ndNgoc1310/Embedded-System-Project/3. Firmware Design/Mylibrary/inc/GUI_Paint.h

/******************************************************************************
* | File      	:   GUI_Paint.h
* | Author      :   Waveshare electronics
* | Function    :	Achieve drawing: draw points, lines, boxes, circles and
*                   their size, solid dotted line, solid rectangle hollow
*                   rectangle, solid circle hollow circle.
* | Info        :
*   Achieve display characters: Display a single character, string, number
*   Achieve time display: adaptive size display time minutes and seconds
*----------------
* |	This version:   V3.0
* | Date        :   2019-04-18
* | Info        :
* -----------------------------------------------------------------------------
* V3.0(2019-04-18):
* 1.Change: 
*    Paint_DrawPoint(..., DOT_STYLE DOT_STYLE)
* => Paint_DrawPoint(..., DOT_STYLE Dot_Style)
*    Paint_DrawLine(..., LINE_STYLE Line_Style, DOT_PIXEL Dot_Pixel)
* => Paint_DrawLine(..., DOT_PIXEL Line_width, LINE_STYLE Line_Style)
*    Paint_DrawRectangle(..., DRAW_FILL Filled, DOT_PIXEL Dot_Pixel)
* => Paint_DrawRectangle(..., DOT_PIXEL Line_width, DRAW_FILL Draw_Fill)
*    Paint_DrawCircle(..., DRAW_FILL Draw_Fill, DOT_PIXEL Dot_Pixel)
* => Paint_DrawCircle(..., DOT_PIXEL Line_width, DRAW_FILL Draw_Filll)
*
* -----------------------------------------------------------------------------
* V2.0(2018-11-15):
* 1.add: Paint_NewImage()
*    Create an image's properties
* 2.add: Paint_SelectImage()
*    Select the picture to be drawn
* 3.add: Paint_SetRotate()
*    Set the direction of the cache    
* 4.add: Paint_RotateImage() 
*    Can flip the picture, Support 0-360 degrees, 
*    but only 90.180.270 rotation is better
* 4.add: Paint_SetMirroring() 
*    Can Mirroring the picture, horizontal, vertical, origin
* 5.add: Paint_DrawString_CN() 
*    Can display Chinese(GB1312)   
*
* ----------------------------------------------------------------------------- 
* V1.0(2018-07-17):
*   Create library
*
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
******************************************************************************/
#ifndef __GUI_PAINT_H
#define __GUI_PAINT_H

#include "DEV_Config.h"
#include "fonts.h"
#include "stdbool.h"

/**
 * Image attributes
**/
typedef struct {
    UBYTE *Image;
    UWORD Width;
    UWORD Height;
    UWORD WidthMemory;
    UWORD HeightMemory;
    UWORD Color;
    UWORD Rotate;
    UWORD Mirror;
    UWORD WidthByte;
    UWORD HeightByte;
    UWORD Scale;
} PAINT;
extern PAINT Paint;

/**
 * Display rotate
**/
#define ROTATE_0            0
#define ROTATE_90           90
#define ROTATE_180          180
#define ROTATE_270          270

/**
 * Display Flip
**/
typedef enum {
    MIRROR_NONE  = 0x00,
    MIRROR_HORIZONTAL = 0x01,
    MIRROR_VERTICAL = 0x02,
    MIRROR_ORIGIN = 0x03,
} MIRROR_IMAGE;
#define MIRROR_IMAGE_DFT MIRROR_NONE

/**
 * image color
**/
#define WHITE          0xFF
#define BLACK          0x00
#define RED            BLACK

#define IMAGE_BACKGROUND    WHITE
#define FONT_FOREGROUND     BLACK
#define FONT_BACKGROUND     WHITE

#define TRUE 1
#define FALSE 0

//4 Gray level
#define  GRAY1 0x03 //Blackest
#define  GRAY2 0x02
#define  GRAY3 0x01 //gray
#define  GRAY4 0x00 //white

/**
 * The size of the point
**/
typedef enum {
    DOT_PIXEL_1X1  = 1,		// 1 x 1
    DOT_PIXEL_2X2  , 		// 2 X 2
    DOT_PIXEL_3X3  ,		// 3 X 3
    DOT_PIXEL_4X4  ,		// 4 X 4
    DOT_PIXEL_5X5  , 		// 5 X 5
    DOT_PIXEL_6X6  , 		// 6 X 6
    DOT_PIXEL_7X7  , 		// 7 X 7
    DOT_PIXEL_8X8  , 		// 8 X 8
} DOT_PIXEL;
#define DOT_PIXEL_DFT  DOT_PIXEL_1X1  //Default dot pilex

/**
 * Point size fill style
**/
typedef enum {
    DOT_FILL_AROUND  = 1,		// dot pixel 1 x 1
    DOT_FILL_RIGHTUP  , 		// dot pixel 2 X 2
} DOT_STYLE;
#define DOT_STYLE_DFT  DOT_FILL_AROUND  //Default dot pilex

/**
 * Line style, solid or dashed
**/
typedef enum {
    LINE_STYLE_SOLID = 0,
    LINE_STYLE_DOTTED,
} LINE_STYLE;

/**
 * Whether the graphic is filled
**/
typedef enum {
    DRAW_FILL_EMPTY = 0,
    DRAW_FILL_FULL,
} DRAW_FILL;

/**
 * Custom structure of a time attribute
**/
typedef struct {
    UWORD Year;  //0000
    UBYTE  Month; //1 - 12
    UBYTE  Day;   //1 - 30
    UBYTE  Hour;  //0 - 23
    UBYTE  Min;   //0 - 59
    UBYTE  Sec;   //0 - 59
} PAINT_TIME;
extern PAINT_TIME sPaint_time;
/**
 * USER follow structure
**/
/* System mode*/
typedef enum {
    DEFAULT_MODE,
    TIME_SETUP_MODE,
    ALARM_SETUP_MODE,
    ALARM_VIEW_MODE,
    ALARM_ACTIVE_MODE,
    SYSTEM_OPTIONS_MODE
  } SYSTEM_MODE;
  extern SYSTEM_MODE sSystem_mode;
  // flag system to detect
  typedef struct 
{
  uint8_t flag_DEFAULT_MODE;
  uint8_t flag_TIME_SETUP_MODE;
  uint8_t flag_ALARM_VIEW_MODE;
  uint8_t flag_ALARM_SETUP_MODE;
  uint8_t flag_SYSTEM_SETUP_MODE;
} FLAG_SYSTEM;
extern FLAG_SYSTEM flag_sSystem_mode;
/*Time alarm setup mode */
// ALARM_DY_DT_MODE
typedef enum
{
  DAY_OF_WEEK_MODE,
  DATE_OF_MONTH_MODE,
  NOT_USED_MODE
} ALARM_DY_DT_MODE;
// struct parameter
typedef struct
{
  uint8_t           second;   // Seconds: 0-59
  uint8_t           minute;   // Minutes: 0-59
  uint8_t           hour;     // Hours: 0-23
  ALARM_DY_DT_MODE  dy_dt; 
  uint8_t           dow_dom;      // Date of the month: 1-31, or Day of the week: 1-7, or not used: 0
  bool              on_off;   // true = ON, false = OFF
} ALARM_DATA_SETUP_MODE;

extern ALARM_DATA_SETUP_MODE sParam_data_alarm_setup_mode_1;
extern ALARM_DATA_SETUP_MODE sParam_data_alarm_setup_mode_2;
extern ALARM_DATA_SETUP_MODE sParam_data_alarm_setup_mode_3;
extern ALARM_DATA_SETUP_MODE sParam_data_alarm_setup_mode_4;
extern ALARM_DATA_SETUP_MODE sParam_data_alarm_setup_mode_5;
extern ALARM_DATA_SETUP_MODE sParam_data_alarm_setup_mode_6;
extern ALARM_DATA_SETUP_MODE sParam_data_alarm_setup_mode_7;
extern ALARM_DATA_SETUP_MODE sParam_data_alarm_setup_mode_8;
extern ALARM_DATA_SETUP_MODE sParam_data_alarm_setup_mode_9;
extern ALARM_DATA_SETUP_MODE sParam_data_alarm_setup_mode_10;
// system view
typedef struct 
{
    ALARM_DATA_SETUP_MODE *sParam_data_alarm_setup_mode_1;
    ALARM_DATA_SETUP_MODE *sParam_data_alarm_setup_mode_2;
    ALARM_DATA_SETUP_MODE *sParam_data_alarm_setup_mode_3;
    ALARM_DATA_SETUP_MODE *sParam_data_alarm_setup_mode_4;
    ALARM_DATA_SETUP_MODE *sParam_data_alarm_setup_mode_5;
    ALARM_DATA_SETUP_MODE *sParam_data_alarm_setup_mode_6;
    ALARM_DATA_SETUP_MODE *sParam_data_alarm_setup_mode_7;
    ALARM_DATA_SETUP_MODE *sParam_data_alarm_setup_mode_8;
    ALARM_DATA_SETUP_MODE *sParam_data_alarm_setup_mode_9;
    ALARM_DATA_SETUP_MODE *sParam_data_alarm_setup_mode_10;
} SYSTEM_PARAM_DATA_ALARM_VIEW_MODE;

extern SYSTEM_PARAM_DATA_ALARM_VIEW_MODE sParam_data_alarm_view_mode;

// Time set up
typedef struct 
{
	uint8_t second;       // Seconds: 0-59
	uint8_t minute;       // Minutes: 0-59
	uint8_t hour;         // Hours: 0-23    
	uint8_t dayofweek;    // Day of the week: 1-7 (1 = Sunday, 2 = Monday, ..., 7 = Saturday)
	uint8_t dateofmonth;  // Date of the month: 1-31
	uint8_t month;        // Month: 1-12
	uint8_t year;         // Year: 0-99 (0 = 2000, 1 = 2001, ..., 99 = 2099)
} TIME_DATA;
extern TIME_DATA time_get_data;
// TIME SET UP
typedef struct
{
  uint8_t           minute;   // Minutes: 0-59
  uint8_t           hour;     // Hours: 0-23
  uint8_t           dow;      // Day of the week: 1-7 (1 = Sunday, 2 = Monday, ..., 7 = Saturday), or Date of the month: 1-31
  uint8_t           dom;      // Date of the month: 1-31, or Day of the week: 1-7, or not used: 0
  uint8_t           month;    // Month: 1-12
  uint8_t           year;     // Year: 0-99 (0 = 2000, 1 = 2001, ..., 99 = 2099)
} TIME_SETUP_DATA;
extern TIME_SETUP_DATA time_setup_data;
// TIme set cursor
typedef enum
{
  TIME_MINUTE,   // Set minutes value
  TIME_HOUR,     // Set hours value
  TIME_DOW,      // Set day of the week value
  TIME_DOM,      // Set date of the month value
  TIME_MONTH,    // Set month value
  TIME_YEAR,     // Set year value
} TIME_SETUP_CURSOR;
// ALARM SETUP CURSOR
typedef enum
{
  ALARM_MINUTE,   // Set minutes value
  ALARM_HOUR,     // Set hours value
  ALARM_DY_DT,    // Set day of week or date of month (1 = day of week, 0 = date of month, 2 = not used)
  ALARM_DOW_DOM,  // Set day of the week or date of the month value
  ALARM_ON_OFF,   // Set ON/OFF state
} ALARM_SETUP_CURSOR;
// SYSTEM_OPT_CURSOR
typedef enum
{
  CLEAR_ALL_ALARM,
  CONTRIBUTOR_INFO,
} SYSTEM_OPT_CURSOR;

// SYSTEM STATE
typedef struct
{
  SYSTEM_MODE         mode;               // Current system mode
  SYSTEM_MODE         past_mode;          // Previous system mode
  TIME_SETUP_CURSOR   time_setup_cursor;  // Cursor of selection for Time Setup Mode
  ALARM_SETUP_CURSOR  alarm_setup_cursor; // Cursor of selection for Alarm Setup Mode
  uint8_t             alarm_view_cursor;  // Cursor of selection for Alarm View Mode
  SYSTEM_OPT_CURSOR   system_opt_cursor;  // Cursor of selection for System Options Mode
  uint8_t             battery_display;    // Battery percentage to be displayed: 100, 75, 50, 25, 0
} SYSTEM_STATE;
extern SYSTEM_STATE system_state;
// ALARM_SETUP_DATA
typedef struct
{
  uint8_t           minute;   // Minutes: 0-59
  uint8_t           hour;     // Hours: 0-23
  ALARM_DY_DT_MODE  dy_dt;    // Select: DAY_OF_WEEK_MODE, DATE_OF_MONTH_MODE, NOT_USED_MODE
  uint8_t           dow_dom;  // Day of the week: 1-7 (1 = Sunday, 2 = Monday, ..., 7 = Saturday), or Date of the month: 1-31
  bool              on_off;   // true = ON, false = OFF
} ALARM_SETUP_DATA;
extern ALARM_SETUP_DATA alarm_setup_data;
//init and Clear
void Paint_NewImage(UBYTE *image, UWORD Width, UWORD Height, UWORD Rotate, UWORD Color);
void Paint_SelectImage(UBYTE *image);
void Paint_SetRotate(UWORD Rotate);
void Paint_SetMirroring(UBYTE mirror);
void Paint_SetPixel(UWORD Xpoint, UWORD Ypoint, UWORD Color);
void Paint_SetScale(UBYTE scale);

void Paint_Clear(UWORD Color);
void Paint_ClearWindows(UWORD Xstart, UWORD Ystart, UWORD Xend, UWORD Yend, UWORD Color);

//Drawing
void Paint_DrawPoint(UWORD Xpoint, UWORD Ypoint, UWORD Color, DOT_PIXEL Dot_Pixel, DOT_STYLE Dot_FillWay);
void Paint_DrawLine(UWORD Xstart, UWORD Ystart, UWORD Xend, UWORD Yend, UWORD Color, DOT_PIXEL Line_width, LINE_STYLE Line_Style);
void Paint_DrawRectangle(UWORD Xstart, UWORD Ystart, UWORD Xend, UWORD Yend, UWORD Color, DOT_PIXEL Line_width, DRAW_FILL Draw_Fill);
void Paint_DrawCircle(UWORD X_Center, UWORD Y_Center, UWORD Radius, UWORD Color, DOT_PIXEL Line_width, DRAW_FILL Draw_Fill);

//Display string
void Paint_DrawChar(UWORD Xstart, UWORD Ystart, const char Acsii_Char, sFONT* Font, UWORD Color_Foreground, UWORD Color_Background);
void Paint_DrawString_EN(UWORD Xstart, UWORD Ystart, const char * pString, sFONT* Font, UWORD Color_Foreground, UWORD Color_Background);
void Paint_DrawString_CN(UWORD Xstart, UWORD Ystart, const char * pString, cFONT* font, UWORD Color_Foreground, UWORD Color_Background);
void Paint_DrawNum(UWORD Xpoint, UWORD Ypoint, int32_t Nummber, sFONT* Font, UWORD Color_Foreground, UWORD Color_Background);
void Paint_DrawNumDecimals(UWORD Xpoint, UWORD Ypoint, double Nummber, sFONT* Font, UWORD Digit, UWORD Color_Foreground, UWORD Color_Background); // Able to display decimals
void Paint_DrawTime(UWORD Xstart, UWORD Ystart, PAINT_TIME *pTime, sFONT* Font, UWORD Color_Foreground, UWORD Color_Background);

//pic
void Paint_DrawBitMap(const unsigned char* image_buffer);
void Paint_DrawBitMap_Paste(const unsigned char* image_buffer, UWORD Xstart, UWORD Ystart, UWORD imageWidth, UWORD imageHeight, UBYTE flipColor);
//void Paint_DrawBitMap_Half(const unsigned char* image_buffer, UBYTE Region);
//void Paint_DrawBitMap_OneQuarter(const unsigned char* image_buffer, UBYTE Region);
//void Paint_DrawBitMap_OneEighth(const unsigned char* image_buffer, UBYTE Region);
void Paint_DrawBitMap_Block(const unsigned char* image_buffer, UBYTE Region);
#endif
